AstroJays-Hopkins/Retired-Avionics/propulsion/ValveControl/RFHybridController/const-common.h

#ifndef __CONST_COMMON_H__
#define __CONST_COMMON_H__

namespace rkt {
    const uint8_t ADDR_GS    = 0b0000;
    const uint8_t ADDR_RKT   = 0b0001;
    const uint8_t ADDR_RB    = 0b0010;
    const uint8_t ADDR_BCAST = 0b1111;

    const uint8_t PKT_NOOP          =   0;
    const uint8_t PKT_GS_STATE_SYNC =   1;
    const uint8_t PKT_HEARTBEAT     =   2;
    const uint8_t PKT_ACK           = 100;
    const uint8_t PKT_NACK          = 101;

    const uint8_t       HB_MAX_MISSED =   12;
    const unsigned long HB_INT        = 2500;

    const uint8_t      CS_MAX_RETRIES    =   3;
    const unsigned int CS_BLINK_INT      = 100;
    const unsigned int CS_RESEND_INT     = 700;
   
    // standard valve commands
    const uint8_t CMD_V_NOOP  = 0;
    const uint8_t CMD_V_CLOSE = 1;
    const uint8_t CMD_V_OPEN  = 2;
    // special "valve" command to ignite
    const uint8_t CMD_V_IGNITE = 255;
}

#endif
