AstroJays-Hopkins/Retired-Avionics/propulsion/ValveControl/RFValves.ino

#include <LoRa.h>

//declare pins for solenoid relays
const int fuelRelay = 4;
const int ventRelay = 5;
const int dcRelay = 6;
const int resetRelay = 7;



void setup() {
  Serial.begin(9600);
  //begin RF communication
  LoRa.begin(915E6);

  //set relay pins to output voltage
  pinMode(ventRelay,OUTPUT);
  // pinMode(dcRelay,OUTPUT);
  pinMode(resetRelay,OUTPUT);

  //set default relay states to LOW (default)
  digitalWrite(ventRelay,LOW);
  digitalWrite(dcRelay,LOW);
  digitalWrite(resetRelay,LOW);
}
void vent() { //open venting solenoid
  digitalWrite(ventRelay,HIGH);
  Serial.println("VENTING");
}

void stopvent() { // close venting solenoid
  digitalWrite(ventRelay,HIGH);
  Serial.println("NOT VENTING");
}

/* void DC() { //disconnect fueling line */
/*   digitalWrite(dcRelay,HIGH); */
/*   Serial.println("DISCONNECTING FUELING LINE"); */
/* } */

/* void RESET() { //reset fueling line linear actuator */
/*   digitalWrite(resetRelay,HIGH); */
/*   Serial.println("RESETTING FUELING LINE"); */
/* } */

void FUEL() { //open fueling valve
  digitalWrite(fuelRelay,HIGH);
  Serial.println("FUELING VALVE OPEN");
}

void DONE() { //close fueling valve
  digitalWrite(fuelRelay,LOW);
  Serial.println("FUELING VALVE CLOSED");
}

void CLOSE() { //close all valves
  digitalWrite(fuelRelay,LOW);
  // digitalWrite(resetRelay,LOW);
  digitalWrite(ventRelay,LOW);
  Serial.println("ALL VALVES CLOSED");
}

void loop() {
  //set variable for received RF command
  String rfInput;
  int packetSize = LoRa.parsePacket();
  if (packetSize){ //receive RF commands
    while (LoRa.available()) {
      rfInput += (char)LoRa.read(); //append string with each solenoid state condition
    }  
  }
  delay(1);
  Serial.println(rfInput); //DEBUG: display RF command

  //set desired states for solenoids as determined by RF command
  if(rfInput[0] == 'V'){ //vent when indicated
    vent();
  } else if (rfInput[0] == 'X') {
    stopvent();
  }
  
  if(rfInput[1] == 'O'){ //disconnect/reset fueling line adapter when desired
    FUEL();
  }else if(rfInput[1] == 'C'){
    DONE();
  }

  if(rfInput[2] == 'I'){ //close all valves after ignition command is given
    CLOSE();
  }
}
